zmeiresearch/DeWille/Software/Control/ESP32_PlatformIO/src/webserver.cpp

/*==============================================================================
   DeWille ESP32 firmware

   Copyright 2020 Ivan Vasilev, Zmei Research Ltd.

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
   THE SOFTWARE IS PROVIDED "AS IS", WITHOUT WARRANTY OF ANY KIND, EXPRESS OR
   IMPLIED, INCLUDING BUT NOT LIMITED TO THE WARRANTIES OF MERCHANTABILITY,
   FITNESS FOR A PARTICULAR PURPOSE AND NONINFRINGEMENT. IN NO EVENT SHALL THE
   AUTHORS OR COPYRIGHT HOLDERS BE LIABLE FOR ANY CLAIM, DAMAGES OR OTHER
   LIABILITY, WHETHER IN AN ACTION OF CONTRACT, TORT OR OTHERWISE, ARISING FROM,
   OUT OF OR IN CONNECTION WITH THE SOFTWARE OR THE USE OR OTHER DEALINGS IN THE
   SOFTWARE.
  ============================================================================*/

//==============================================================================
//  Includes
//==============================================================================
#include <WiFi.h>
#include <WiFiClient.h>
#include <ESPmDNS.h>
#include <Update.h>
#include "SPIFFS.h"
#include "ESPAsyncWebServer.h"

#include "config.h"

//==============================================================================
//  Defines
//==============================================================================

//==============================================================================
//  Local types
//==============================================================================

//==============================================================================
//  Local data
//==============================================================================
static AsyncWebServer server(80);

//==============================================================================
//  Local function definitions
//==============================================================================
static void notFoundResponse(AsyncWebServerRequest *request);
static void firmwareUpload(AsyncWebServerRequest *request, String filename, size_t index, uint8_t *data, size_t len, bool final);
static void spiffsUpload(AsyncWebServerRequest *request, String filename, size_t index, uint8_t *data, size_t len, bool final);


//==============================================================================
//  Local functions
//==============================================================================

// 404 default handler
static void notFoundResponse(AsyncWebServerRequest *request)
{
    request->send(404, "text/plain", "Not found");
}

// IVA: TODO: Merge firmwareUpload and spiffsUpload - the two differ only in U_FLASH/U_SPIFFS
// Firmware upload
static void firmwareUpload(AsyncWebServerRequest *request, String filename, size_t index, uint8_t *data, size_t len, bool final)
{
    // handle upload and update
    if (!index)
    {
        Serial.printf("Update: %s\n", filename.c_str());
        if (!Update.begin(UPDATE_SIZE_UNKNOWN, U_FLASH))
        { 
            //start with max available size
            Update.printError(Serial);
        }
    }

    /* flashing firmware to ESP*/
    if (len)
    {
        Update.write(data, len);
    }

    if (final)
    {
        if (Update.end(true))
        { 
            //true to set the size to the current progress
            Serial.printf("Update Success: %ub written\nRebooting...\n", index+len);
        }
        else
        {
            Update.printError(Serial);
        }
    }
}

// SPIFFS upload
static void spiffsUpload(AsyncWebServerRequest *request, String filename, size_t index, uint8_t *data, size_t len, bool final)
{
    if (!index)
    {
        Serial.printf("Update: %s\n", filename.c_str());
        if (!Update.begin(UPDATE_SIZE_UNKNOWN, U_SPIFFS))
        { 
            Update.printError(Serial);
        }
    }

    if (len)
    {
        Update.write(data, len);
    }

    if (final)
    {
        if (Update.end(true))
        { 
            Serial.printf("Update Success: %ub written\nRebooting...\n", index+len);
        }
        else
        {
            Update.printError(Serial);
        }
    }
}

//==============================================================================
//  Exported functions
//==============================================================================

// Initialize update webserver
void WebserverInit(void * params) 
{
    // IVA: TODO: Use Logger instead!
    Serial.begin(115200);

    // IVA: TODO: Move SPIFFS and Wifi intialization outside!
    if (!SPIFFS.begin())
    {
        Serial.println("An Error has occurred while mounting SPIFFS");
        return;
    }

    // Connect to WiFi network
    WiFi.begin(WIFI_SSID, WIFI_PASSWORD);
    Serial.println("");

    // Wait for connection
    while (WiFi.status() != WL_CONNECTED) 
    {
        // IVA: TODO: Use FreeRTOS primitives!
        delay(500);
        Serial.print(".");
    }
  
    Serial.println("");
    Serial.print("Connected to ");
    Serial.println(WIFI_SSID);
    Serial.print("IP address: ");
    Serial.println(WiFi.localIP());

    // Advertise through MDNS
    if (!MDNS.begin(DEVICE_NAME)) 
    {
        Serial.println("Error setting up MDNS responder!");
    }

    Serial.println("mDNS responder started");
    
    // Web root 
    server.on("/", HTTP_GET, [](AsyncWebServerRequest *request) {
        AsyncWebServerResponse *response = request->beginResponse(SPIFFS, "/index.html", "text/html");
        response->addHeader("Connection", "close");
        request->send(response);

    });

    // Firmware update handler
    server.on("/updateFirmware", HTTP_POST, [](AsyncWebServerRequest *request) {
        if (!Update.hasError()) {
            AsyncWebServerResponse *response = request->beginResponse(200, "text/plain", "OK");
            response->addHeader("Connection", "close");
            request->send(response);
            ESP.restart();
        } else {
            AsyncWebServerResponse *response = request->beginResponse(500, "text/plain", "ERROR");
            response->addHeader("Connection", "close");
            request->send(response);
        } }, firmwareUpload);

    // SPIFFS update handler
    server.on("/updateSpiffs", HTTP_POST, [](AsyncWebServerRequest *request) {
        if (!Update.hasError()) {
            AsyncWebServerResponse *response = request->beginResponse(200, "text/plain", "OK");
            response->addHeader("Connection", "close");
            request->send(response);
            ESP.restart();
        } else {
            AsyncWebServerResponse *response = request->beginResponse(500, "text/plain", "ERROR");
            response->addHeader("Connection", "close");
            request->send(response);
        } }, spiffsUpload);

    // serve static files directly
    server.serveStatic("/static", SPIFFS, "/static/");


    // Everything else - 404
    server.onNotFound(notFoundResponse);
   
    server.begin();
}
